maximevince/PicoZorro/firmware/pz-app/src/bin/nic-demo.rs

//! Ethernet chip check: bring the chip up on SPI1, get a DHCP lease, answer
//! pings and echo TCP on port 7. The embassy-net stack is only a test tool
//! here; the product firmware moves raw frames between the Zorro side and
//! the chip.
//!
//! Wiring and chip features: `pz_hal::chip` (`pz-hal/src/chip.rs`).
//! Flash and watch: `cargo run --release --bin nic-demo` (probe-rs, defmt over RTT).
#![no_std]
#![no_main]

use defmt::{info, unwrap, warn};
use embassy_executor::Spawner;
use embassy_net::tcp::{TcpListener, TcpSocket};
use embassy_net::{Stack, StackStorage};
use embassy_rp::clocks::RoscRng;
use embassy_time::{Duration, Timer};
use embedded_io_async::Write;
use pz_hal::{chip, chip_pins};
use static_cell::StaticCell;
use {defmt_rtt as _, panic_probe as _};


#[embassy_executor::task]
async fn net_task(mut runner: embassy_net::Runner<'static>) -> ! {
    runner.run().await
}

#[embassy_executor::main]
async fn main(spawner: Spawner) {
    let p = embassy_rp::init(Default::default());
    info!("PicoZorro nic-demo");

    let chip_id = match embassy_rp::otp::get_chipid() {
        Ok(id) => id,
        Err(e) => {
            warn!("OTP chip id unreadable ({:?}), using 0", e);
            0
        }
    };
    let mac = pz_core::mac::from_chip_id(chip_id);
    info!("MAC {:02x}:{:02x}:{:02x}:{:02x}:{:02x}:{:02x}", mac[0], mac[1], mac[2], mac[3], mac[4], mac[5]);

    let Some(device) = chip::bring_up(&spawner, chip_pins!(p), mac).await else {
        defmt::panic!("no Ethernet chip on SPI1: check the wiring (hardware/PINMAP.md)");
    };

    static STORAGE: StaticCell<StackStorage> = StaticCell::new();
    let seed = RoscRng.next_u64();
    let (stack, runner) = Stack::new(STORAGE.init(StackStorage::new()), seed);
    static DEVICE: StaticCell<chip::NetDevice> = StaticCell::new();
    let iface = unwrap!(stack.add_iface_borrowed(DEVICE.init(device)).ok());
    unwrap!(iface.set_dhcpv4(Some(Default::default())).ok());
    spawner.spawn(unwrap!(net_task(runner)));

    info!("waiting for link + DHCP");
    iface.wait_link_up().await;
    info!("link up");
    iface.wait_config_up().await;
    let lease = unwrap!(iface.dhcpv4_lease());
    info!("IP {} (ping me), TCP echo on port 7", lease.address.address());

    echo_server(stack).await
}
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
